karthik4j/arduino-clock/clock-dims/back-front.PNG

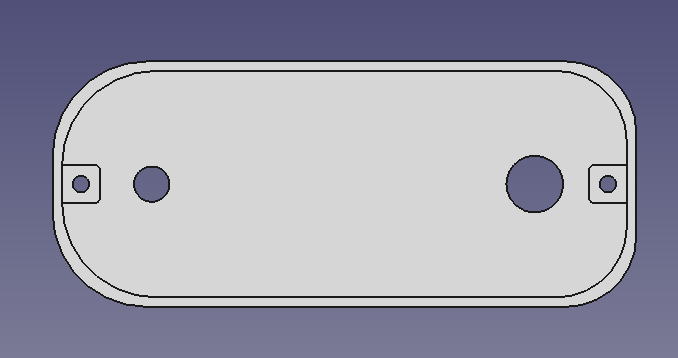
clock-dims/back-front.PNG
