karthik4j/arduino-clock/clock-dims/front-3.png

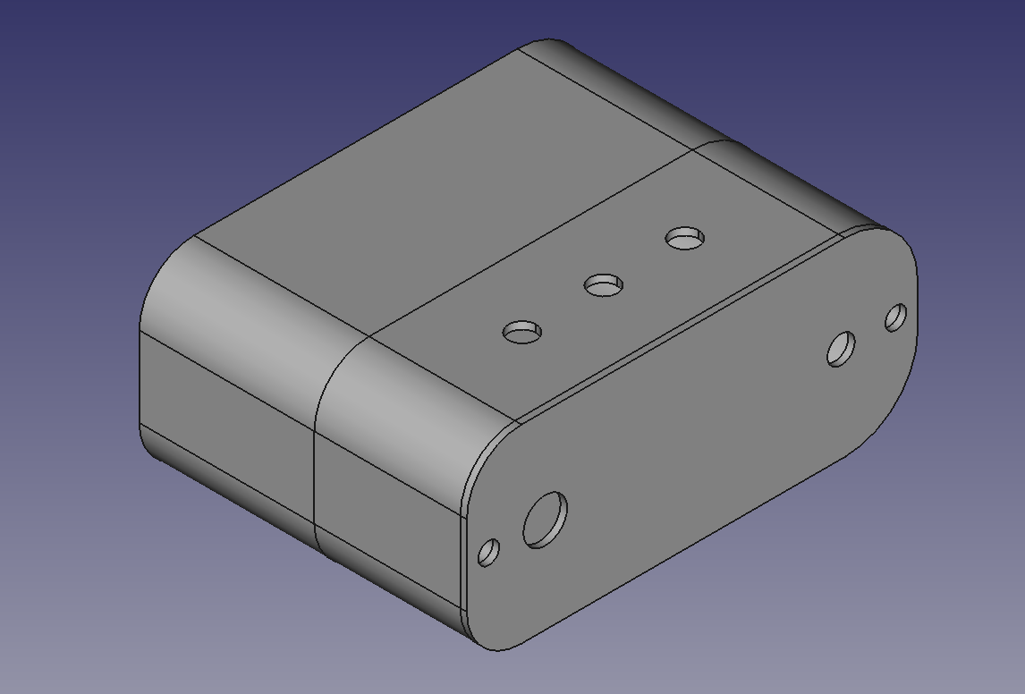
clock-dims/front-3.png
