karthik4j/arduino-clock/clock-dims/front.PNG

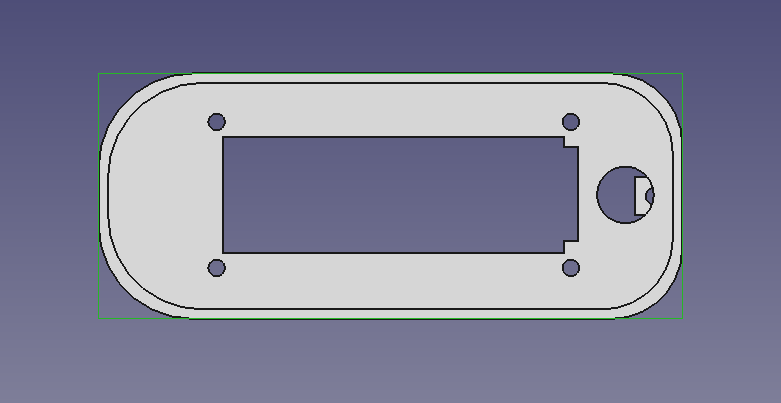
clock-dims/front.PNG
