karthik4j/arduino-clock/clock-dims/full.png

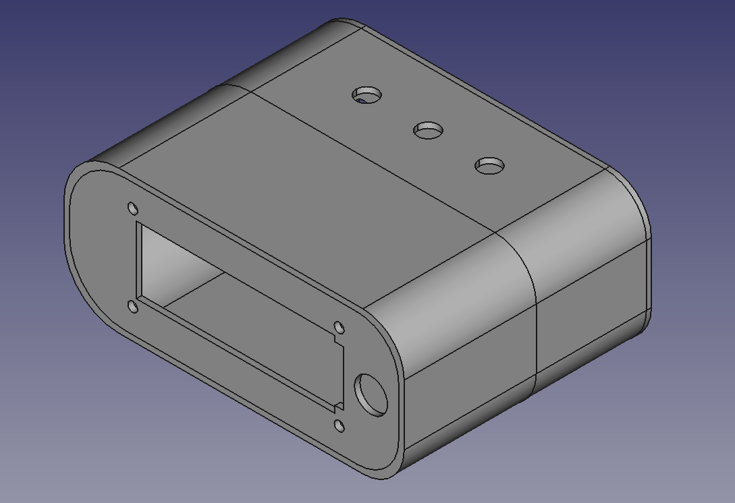
clock-dims/full.png
