karthik4j/arduino-clock/clock-dims/half-front2.png

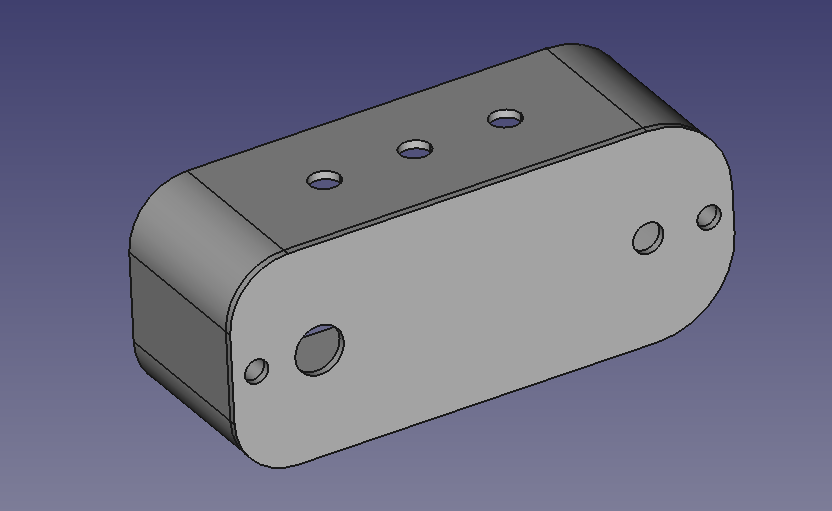
clock-dims/half-front2.png
