karthik4j/arduino-clock/pictures-of-clock/front.jpg

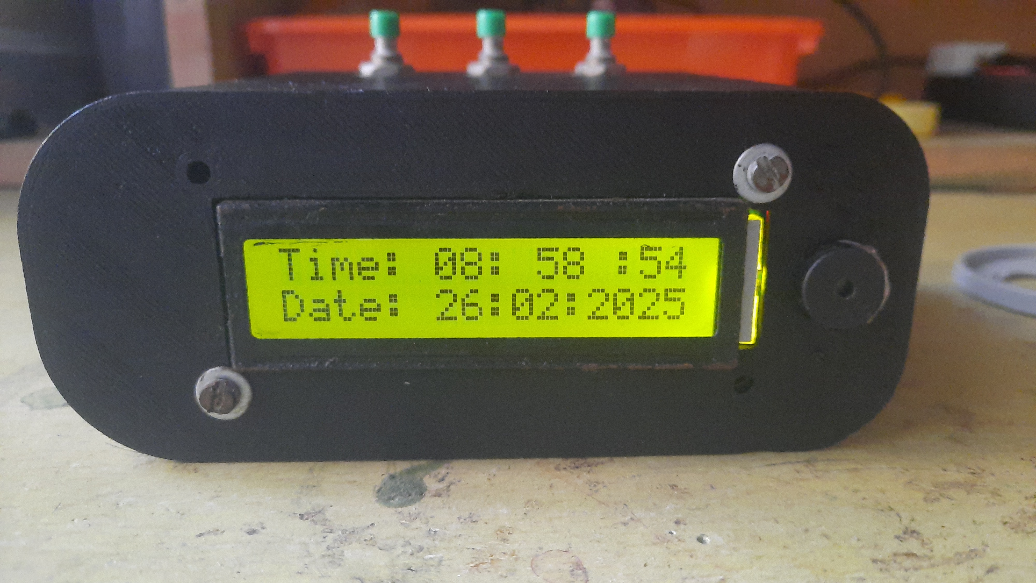
pictures-of-clock/front.jpg
