karthik4j/arduino-clock/pictures-of-clock/inside (1).jpg

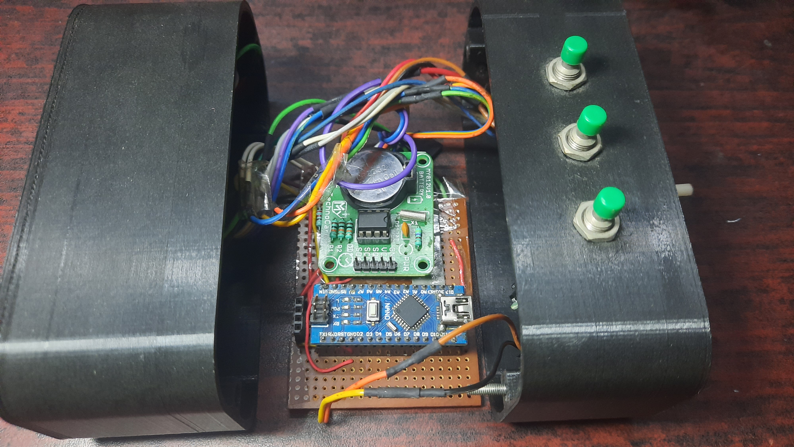
pictures-of-clock/inside (1).jpg
