karthik4j/arduino-clock/pictures-of-clock/inside (2).jpg

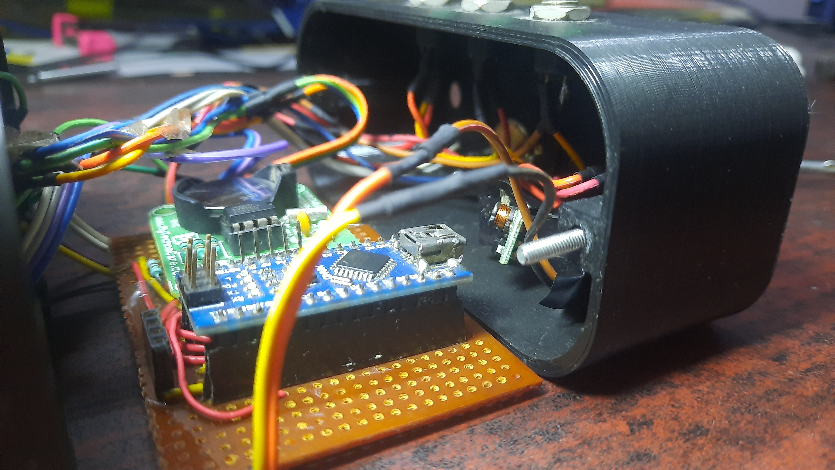
pictures-of-clock/inside (2).jpg
