karthik4j/arduino-clock/pictures-of-clock/inside (3).jpg

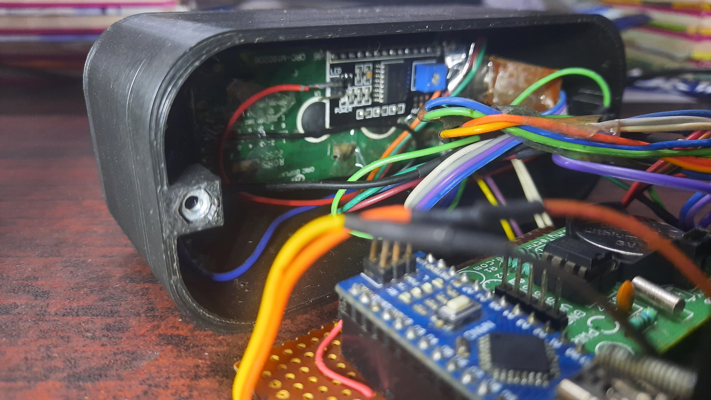
pictures-of-clock/inside (3).jpg
