karthik4j/arduino-clock/pictures-of-clock/side (1).jpg

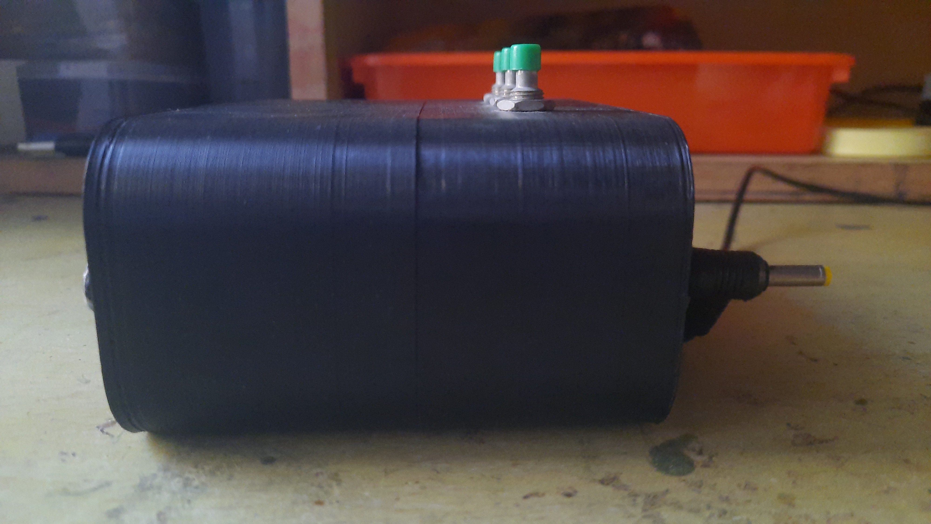
pictures-of-clock/side (1).jpg
