karthik4j/arduino-clock/pictures-of-clock/side (2).jpg

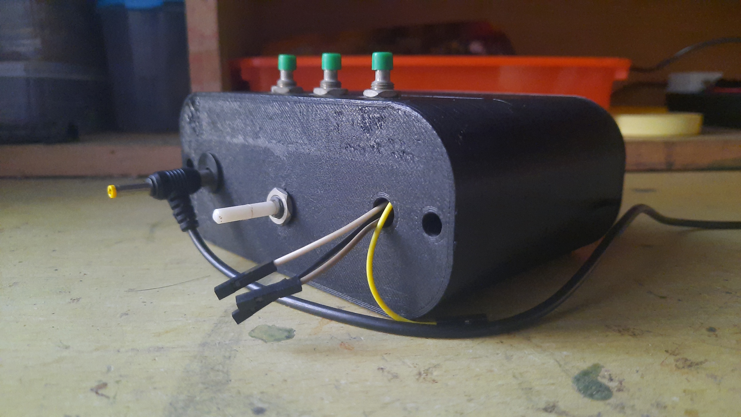
pictures-of-clock/side (2).jpg
