karthik4j/arduino-clock/pictures-of-clock/top (1).jpg

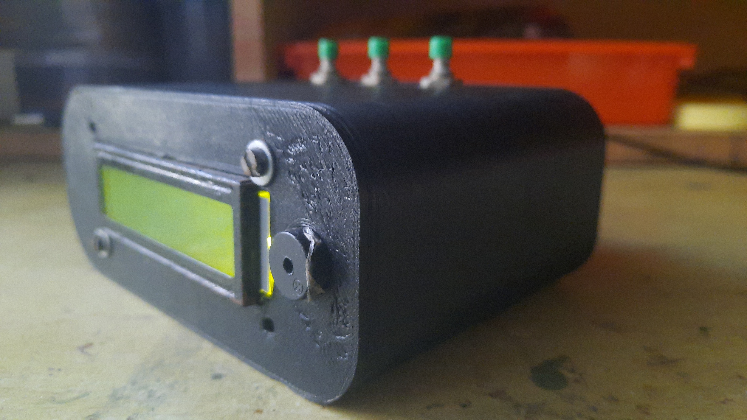
pictures-of-clock/top (1).jpg
