karthik4j/arduino-clock/pictures-of-clock/top (3).jpg

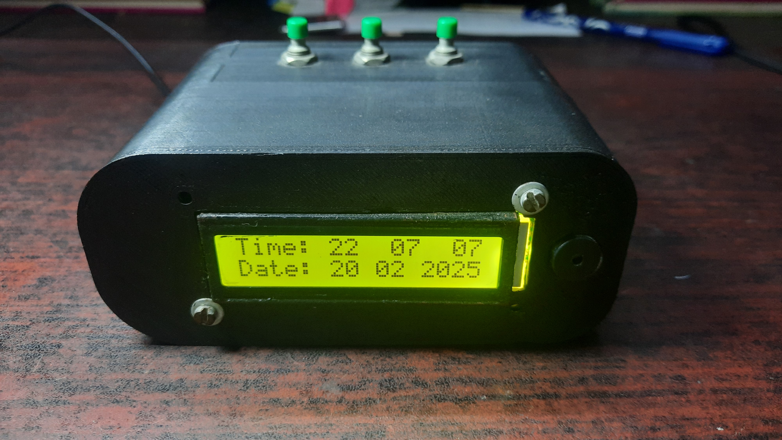
pictures-of-clock/top (3).jpg
